zultron/autoclave_control/qml/autoclave-remote/Autoclave/assets/p0-idle-blue.png

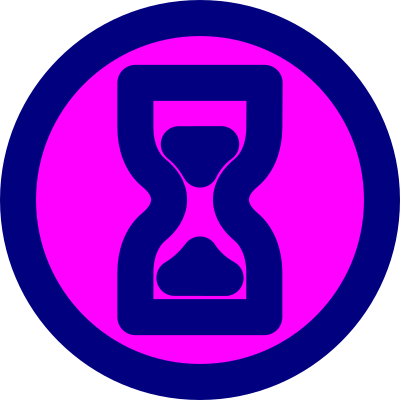
qml/autoclave-remote/Autoclave/assets/p0-idle-blue.png
