zultron/autoclave_control/qml/autoclave-remote/Autoclave/assets/p0-idle-green.png

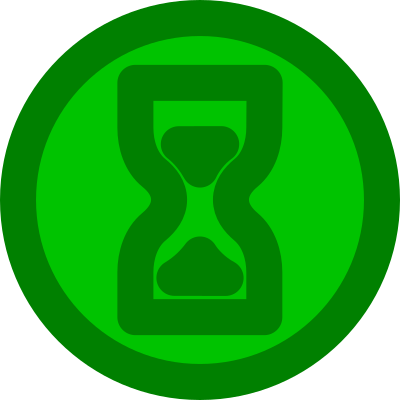
qml/autoclave-remote/Autoclave/assets/p0-idle-green.png
