zultron/autoclave_control/qml/autoclave-remote/Autoclave/assets/p3-heat-blue.png

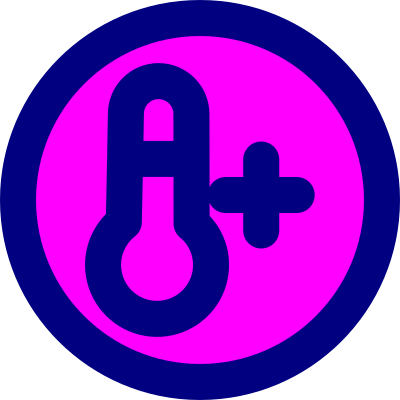
qml/autoclave-remote/Autoclave/assets/p3-heat-blue.png
